kmw3kx/breathController/media/daisypin.png

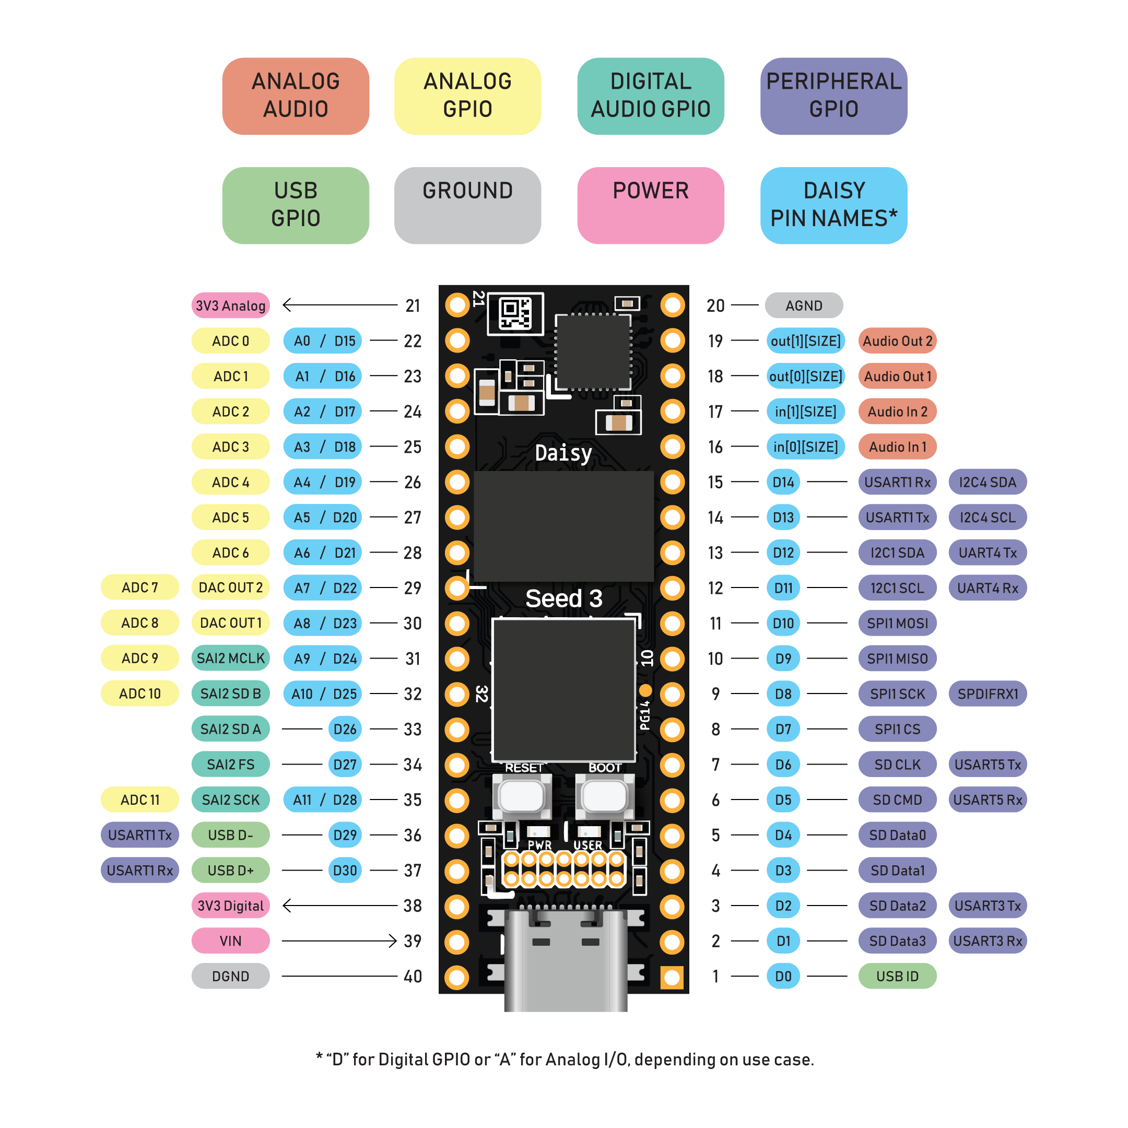
media/daisypin.png
