kmw3kx/breathController/media/PrototypeDaisyEVIClean_Left.jpg

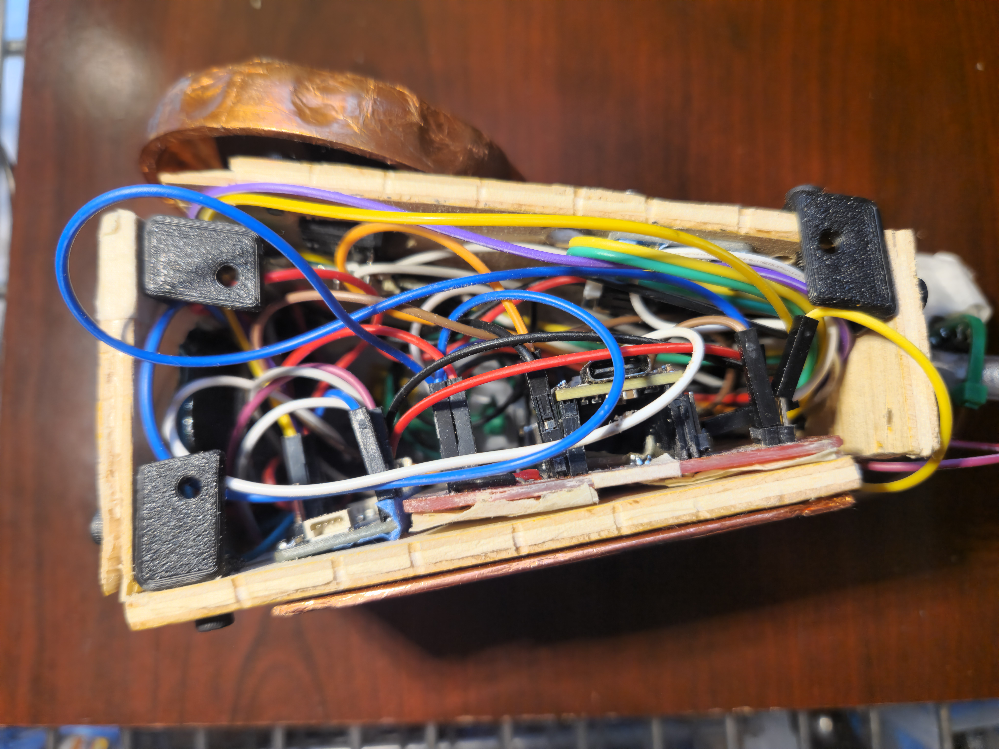
media/PrototypeDaisyEVIClean_Left.jpg
